LaskaKit/ESPD-35/img/004.jpg

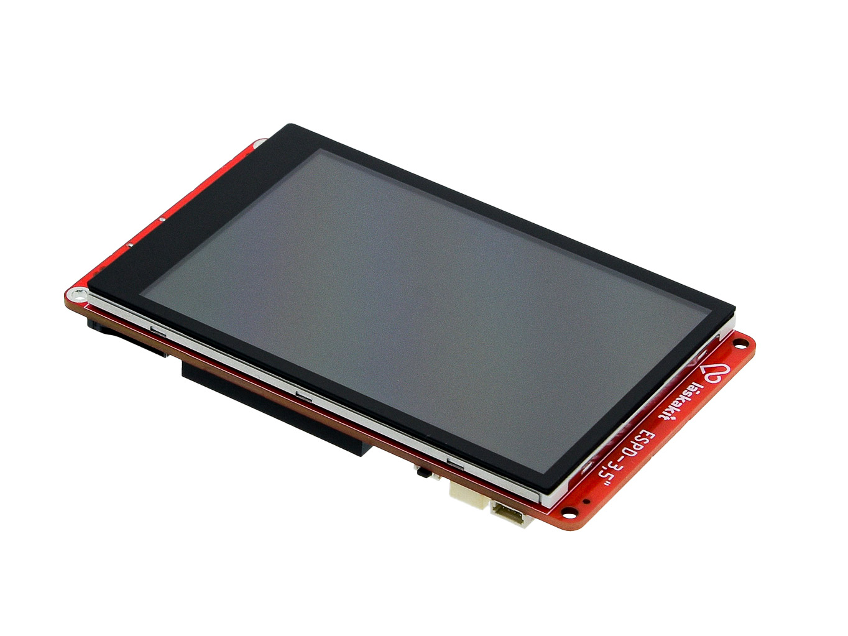
img/004.jpg
