LaskaKit/ESPD-35/img/007.JPG

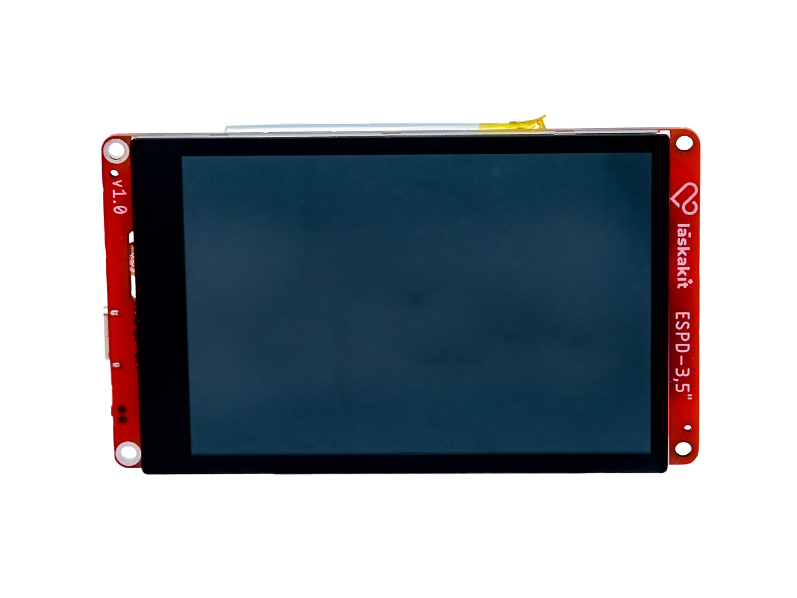
img/007.JPG
