LaskaKit/ESPD-35/SW/ESPD35_MeteoPlaneRadar/src/ADSB.cpp

// =============================================================================
//  ESPD35_MeteoPlaneRadar - ADS-B klient (stahovani dat o letadlech z adsb.fi).
//  Robustni stahovani: cele telo se nacte do PSRAM bufferu a parsuje se az
//  kompletni (kontrola utnuti proti Content-Length + jeden retry), s filtrem
//  ArduinoJson v7. Pri chybe zustava posledni dobry snimek (s_list/s_count se
//  neprepise), takze uriznuty JSON uz radar nevymaze.
//  Zdroj: adsb.fi - zdarma, bez klice, jen pro osobni nekomercni pouziti.
// =============================================================================
#include "ADSB.h"
#include <WiFi.h>
#include <WiFiClientSecure.h>
#include <HTTPClient.h>
#include <ArduinoJson.h>
#include <math.h>
#include <string.h>
#include <stdlib.h>          // strtof
#include "esp_heap_caps.h"   // PSRAM body buffer
#include "NetSink.h"         // cteni tela bezpecne vuci chunked
#include "Net.h"        // strazce interni pameti + hlavicka Date
#include "Status.h"     // jednoradkove hlaseni pro stavovou stranku
#include "Settings.h"   // vyskove pasmo, "jen s volacim znakem"
#include "Config.h"     // SQUAWK_*

static const float KM_PER_NM = 1.852f;

static Aircraft s_list[ADSB_MAX];   // posledni DOBRY snimek na obrazovce
static int s_count = 0;
// Docasny buffer, do ktereho parsujeme. Viditelny seznam (s_list/s_count) se
// prepise az po plnem a spravnem parsu - tak uriznuty JSON nikdy nevymaze radar.
static Aircraft s_tmp[ADSB_MAX];
// Ctverec vzdalenosti kazdeho letadla v s_tmp od stredu (km^2). Slouzi k tomu,
// aby se pri prekroceni ADSB_MAX drzela NEJBLIZSI letadla, ne prvnich sto
// v poradi, ve kterem je posle server (viz smycku parsovani nize).
static float s_tmpD2[ADSB_MAX];
static void (*s_poll)() = nullptr;

// Kolik letadel odfiltrovalo NASTAVENI (ne vzdalenost). Drzi se zvlast, aby
// slo na stavove strance odlisit "nad vami nic nelita" od "mate prisny filtr".
static int s_filteredOut = 0;

void ADSB_SetPollFn(void (*fn)()) { s_poll = fn; }
int  ADSB_Count() { return s_count; }
const Aircraft* ADSB_List() { return s_list; }

int ADSB_FindByHex(const char* hex) {
  if (!hex || !hex[0]) return -1;
  for (int i = 0; i < s_count; i++) {
    if (strcmp(s_list[i].hex, hex) == 0) return i;
  }
  return -1;   // uz neni v datech
}

int ADSB_FilteredOut() { return s_filteredOut; }

const char* ADSB_EmergencyCode(const Aircraft& a) {
  if (!a.squawk[0]) return nullptr;
  if (strcmp(a.squawk, SQUAWK_HIJACK) == 0) return SQUAWK_HIJACK;
  if (strcmp(a.squawk, SQUAWK_RADIO)  == 0) return SQUAWK_RADIO;
  if (strcmp(a.squawk, SQUAWK_EMERG)  == 0) return SQUAWK_EMERG;
  return nullptr;
}

// Projde letadlo uzivatelskym filtrem? Nouzovy squawk filtr PRESKAKUJE -
// letadlo hlasici 7700 je presne to, co chcete videt, i kdyz je zrovna mimo
// nastavene vyskove pasmo.
static bool passesFilter(const Aircraft& a) {
  if (Settings_SquawkAlert() && ADSB_EmergencyCode(a)) return true;
  if (Settings_OnlyWithCallsign() && !a.callsign[0]) return false;
  const uint16_t lo = Settings_AltMinFt();
  const uint16_t hi = Settings_AltMaxFt();
  // Letadlo, ktere vysku vubec nehlasi (altFt == 0), se pasmem neposuzuje -
  // jinak by ho spodni mez vyhodila, aniz by o nem cokoli bylo znamo.
  if (a.altFt > 0.0f) {
    if (a.altFt < (float)lo) return false;
    if (a.altFt > (float)hi) return false;
  }
  return true;
}

static void poll() { if (s_poll) s_poll(); }

// Cte cislo i kdyz je v JSON jako retezec.
static bool readFloat(JsonObjectConst o, const char* key, float* out) {
  JsonVariantConst v = o[key];
  if (v.is<float>() || v.is<double>() || v.is<int>()) { *out = v.as<float>(); return true; }
  if (v.is<const char*>()) {
    // ArduinoJson si ciselny retezec prevede sam, jenze atof() nerozlisi
    // chybejici hodnotu od necislne: z "ground" udelal 0.0 a ohlasil uspech.
    // Koncovy ukazatel u strtof() ten rozdil ukaze, takze necekany literal
    // propadne misto toho, aby se z nej stala nulova vyska.
    const char* str = v.as<const char*>();
    if (!str || !*str) return false;
    char* end = nullptr;
    float f = strtof(str, &end);
    if (end == str) return false;
    *out = f;
    return true;
  }
  return false;
}

// Volacka, a JEN volacka. Drive tu byl zaloznik na hex adresu, aby letadlo,
// ktere volacku nevysila (TIS-B, MLAT, soukrome a vojenske stroje), aspon neco
// ukazalo. To byla chyba: volacka jde do dotazu na trasu a hex adresa se po
// normalizaci tvari jako platne cislo letu - "a31234" se zmeni na "A31234",
// coz je Aegean Airlines 1234, takze letadlo nad Prahou hlasilo let
// Atheny - Istanbul. Bez volacky zustava pole prazdne a na trasu se nikdo
// nepta; kdo potrebuje neco vykreslit, sahne po hexu sam (viz ScreenPlanes).
static void copyCallsign(Aircraft* a, JsonObjectConst plane) {
  const char* src = plane["flight"] | "";
  while (*src == ' ' || *src == '\t') src++;   // adsb.fi doplnuje na osm znaku
  int i = 0;
  while (src[i] && i < (int)sizeof(a->callsign) - 1) { a->callsign[i] = src[i]; i++; }
  while (i > 0 && (a->callsign[i-1] == ' ' || a->callsign[i-1] == '\t')) i--;
  a->callsign[i] = '\0';
}

// -----------------------------------------------------------------------------
//  Buffer tela (PSRAM). Recykluje se mezi stazenimi, aby se interni heap
//  netristil velkym String pri kazdem pollu. Cele telo se nacte SEM pred
//  parsovanim, takze parser vzdy vidi kompletni dokument (puvodni
//  "IncompleteInput" vznikal parsovanim primo z TLS streamu, ktery skoncil
//  uprostred objektu).
// -----------------------------------------------------------------------------
static char*  s_body    = nullptr;
static size_t s_bodyCap = 0;
static const size_t ADSB_MAX_BODY = 1024 * 1024;   // 1 MB tvrdy strop
// Rezervuje se, kdyz server neposle Content-Length (chunked). Pod tvrdym
// stropem, nad vsim, co adsb.fi realne vrati: nejsirsi nabizeny dosah je
// 100 km, kde odpoved ma nizke desitky kB.
static const size_t ADSB_UNKNOWN_BODY = 384 * 1024;

static bool bodyReserve(size_t need) {
  if (need <= s_bodyCap) return true;
  size_t cap = need + 2048;
  char* nb = (char*)heap_caps_realloc(s_body, cap, MALLOC_CAP_SPIRAM);
  if (!nb) nb = (char*)heap_caps_realloc(s_body, cap, MALLOC_CAP_DEFAULT);
  if (!nb) return false;
  s_body = nb; s_bodyCap = cap;
  return true;
}

// Nacte cele telo HTTP do s_body. Vraci pocet bajtu (>= 0), nebo -1 pri tvrde
// chybe: alokace, preteceni, zaseknuti nebo prenos ukonceny driv, nez slibovala
// deklarovana delka.
static long readBody(HTTPClient& http) {
  // writeToStream() dekoduje chunked; rucni smycka nad getStreamPtr() ne, a
  // presne proto zustavaly velikosti bloku v tele.
  int declared = http.getSize();               // -1 kdyz chunked / neznamy
  if (declared > (int)ADSB_MAX_BODY) {
    Serial.printf("ADSB: hlaseno %d B, strop je %u B\n",
                  declared, (unsigned)ADSB_MAX_BODY);
    return -1;
  }
  // Sink zapisuje do pevneho bufferu a neumi ho zvetsit uprostred prenosu,
  // takze chunked odpoved musi dostat misto dopredu. Buffer lezi v PSRAM a
  // recykluje se mezi stazenimi, takze ta rezerva nic nestoji.
  size_t want = (declared > 0) ? (size_t)declared + 1 : ADSB_UNKNOWN_BODY;
  if (!bodyReserve(want)) return -1;

  return Net_ReadBody(http, (uint8_t*)s_body, s_bodyCap, "ADSB", s_poll);
}

// Filtr: parsuji se jen klice, ktere pouzivame, takze JsonDocument zustava maly
// bez ohledu na to, kolik adsb.fi posle. alt_baro MUSI zustat - nese literal
// "ground" pro detekci letadla na zemi.
static void buildFilter(JsonDocument& filter) {
  JsonObject o = filter["ac"].add<JsonObject>();   // ArduinoJson 7 idiom
  o["hex"]          = true;
  o["flight"]       = true;
  o["lat"]          = true;
  o["lon"]          = true;
  o["track"]        = true;
  o["true_heading"] = true;
  o["alt_baro"]     = true;
  o["gs"]           = true;
  o["baro_rate"]    = true;
  o["t"]            = true;
  o["r"]            = true;   // registrace - zadarmo v teze odpovedi
  o["squawk"]       = true;

  // Neni to uzitecny obsah, ale diagnostika: adsb.fi dava svuj stavovy text do
  // "msg" ("No error" pri uspechu). Filtr ho driv zahazoval, takze firmware
  // umel rict jen "chybi pole ac" a nic o tom proc. Prida se az nakonec -
  // pridani klice muze zneplatnit JsonObject vzaty vyse.
  filter["msg"] = true;
}

bool ADSB_Fetch(double lat, double lon, float radiusKm) {
  // Bez pripojeni -> nech, co je na obrazovce (radar NEVYMAZAT).
  if (WiFi.status() != WL_CONNECTED) {
    Serial.println("ADSB: no WiFi");
    Status_Set(ST_ADSB, "bez WiFi");
    return false;
  }
  // TLS handshake potrebuje ~45 kB interni RAM; bez ni selze uvnitr mbedTLS
  // a navenek to vypada jako hole "HTTP -1". Radeji poll preskocit.
  if (!Net_HeapOk("ADSB")) { Status_Set(ST_ADSB, "malo pameti"); return false; }

  float distNm = radiusKm / KM_PER_NM;
  char url[128];
  snprintf(url, sizeof(url), "%s%.5f/lon/%.5f/dist/%.1f",
           ADSB_API_BASE, lat, lon, distNm);
  Serial.printf("ADSB: %s\n", url);

  // Az dva pokusy. Jeden prechodny zadrhel (spadle TLS, uriznute telo) tak
  // nepreskoci cely cyklus; po dvou chybach se propadne a zustane posledni snimek.
  const int MAX_ATTEMPTS = 2;
  for (int attempt = 1; attempt <= MAX_ATTEMPTS; attempt++) {
    poll();
    WiFiClientSecure client;
    client.setInsecure();
    client.setHandshakeTimeout(NET_TLS_HANDSHAKE_S);

    HTTPClient http;
    http.setConnectTimeout(8000);   // ms - jen TCP connect, NE handshake
    http.setTimeout(12000);         // ms - cteni
    http.setReuse(false);
    if (!http.begin(client, url)) {
      Serial.println("ADSB: begin failed");
      if (attempt < MAX_ATTEMPTS) { delay(200); continue; }
      return false;
    }
    // Slusne se predstavit - bezplatne API adsb.fi o to zada.
    // POZOR: setUserAgent(), NE addHeader(). ESP32 HTTPClient::addHeader()
    // mlcky zahazuje Connection, Host, Accept-Encoding a prave User-Agent -
    // vidi je jako "handled by code" a nic nenahlasi. Tahle hlavicka se tedy
    // driv neposilala vubec a odchazela vychozi "ESP32HTTPClient"; adsb.lol na
    // ni odpovida 403 "User-Agent too generic". Jeden retezec pro obe API je
    // v Config.h.
    http.setUserAgent(HTTP_USER_AGENT);
    http.addHeader("Accept", "application/json");
    // Hlavicka Date je zaloha hodin, kdyz NTP neprojde (viz Clock.h).
    http.collectHeaders(NET_DATE_HEADER, 1);

    int code = http.GET();
    if (code != HTTP_CODE_OK) {
      Serial.printf("ADSB: HTTP %d (pokus %d)\n", code, attempt);
      http.end();
      if (attempt < MAX_ATTEMPTS) { delay(200); continue; }
      Status_Set(ST_ADSB, "HTTP %d", code);
      return false;   // nech posledni dobra data
    }
    Net_NoteDate(http);

    // Nacti CELE telo (do PSRAM), pak teprve parsuj - zadny parse ze streamu.
    long len = readBody(http);
    http.end();

    if (len < 0) {
      Serial.println("ADSB: cteni tela selhalo");
      if (attempt < MAX_ATTEMPTS) { delay(200); continue; }
      return false;
    }
    if (len < 8) {
      Serial.printf("ADSB: kratke telo %ld (pokus %d)\n", len, attempt);
      if (attempt < MAX_ATTEMPTS) { delay(200); continue; }
      return false;
    }

    // Levna kontrola tvaru driv, nez to uvidi parser. Chyti chybovou stranku
    // z proxy, gzip nebo zbytky bloku - tedy vsechno, co by jinak doslo az k
    // ArduinoJsonu a vratilo se jako neco nesrozumitelneho.
    const char* head = s_body;
    while (*head == ' ' || *head == '\r' || *head == '\n' || *head == '\t') head++;
    if (*head != '{') {
      Serial.printf("ADSB: odpoved nezacina JSON objektem, telo[0..120]: %.120s\n", s_body);
      Status_Set(ST_ADSB, "neocekavana odpoved");
      return false;
    }

    // Filtrovany parse kompletniho bufferu.
    JsonDocument filter;
    buildFilter(filter);
    JsonDocument doc;
    DeserializationError err =
        deserializeJson(doc, s_body, (size_t)len, DeserializationOption::Filter(filter));
    if (err) {
      Serial.printf("ADSB: JSON %s (pokus %d) - drzim poslednich %d\n",
                    err.c_str(), attempt, s_count);
      if (attempt < MAX_ATTEMPTS) { delay(200); continue; }
      return false;
    }

    if (!doc["ac"].is<JsonArray>()) {
      // Rict, CO prislo, ne jen ze to bylo spatne. "msg" je stavovy text
      // serveru, zacatek tela chyti odpovedi, ktere ocekavany tvar nemely
      // nikdy.
      Serial.printf("ADSB: chybi pole 'ac' - msg: %s\n", doc["msg"] | "(zadne msg)");
      Serial.printf("ADSB: telo[0..200]: %.200s\n", s_body);
      Status_Set(ST_ADSB, "spatny tvar odpovedi");
      return false;   // validni JSON, ale spatny tvar; retry by nepomohl
    }

    // Parsuj do DOCASNEHO seznamu; do ziveho commitni az pri uspechu.
    //
    // Pri prekroceni ADSB_MAX se NEUTINA slepe. Puvodne se pri naplneni pole
    // proste skoncilo (break), takze o tom, ktera letadla uvidite, rozhodovalo
    // poradi v odpovedi serveru - u velkeho rozsahu nad hustym provozem tak
    // mohlo vypadnout letadlo primo nad vami. Nove se drzi NEJBLIZSICH
    // ADSB_MAX letadel: po naplneni pole se nove letadlo porovna s dosud
    // nejvzdalenejsim a pripadne ho nahradi.
    const float latr0 = (float)lat * 0.0174532925f;
    const float cosLat0 = cosf(latr0);

    JsonArrayConst ac = doc["ac"].as<JsonArrayConst>();
    int   n = 0;
    int   worstIdx = -1;      // slot s nejvetsi vzdalenosti (jen kdyz je plno)
    float worstD2  = -1.0f;
    int   dropped  = 0;       // kolik letadel se nevešlo (jen pro vypis)

    s_filteredOut = 0;

    for (JsonObjectConst plane : ac) {
      float plat, plon;
      if (!readFloat(plane, "lat", &plat) || !readFloat(plane, "lon", &plon)) continue;
      // Ochrana proti nesmyslnym souradnicim (NaN projde i porovnanim, proto
      // se testuje pres !(a && b), ne pres opacnou podminku).
      if (!(plat >= -90.0f && plat <= 90.0f && plon >= -180.0f && plon <= 180.0f)) continue;
      if (plat == 0.0f && plon == 0.0f) continue;

      // Letadla NA ZEMI zahazujeme uz tady, aby nikdy nezabrala misto stroji
      // ve vzduchu. U letiste by jinak dokazala zaplnit cely ADSB_MAX.
      JsonVariantConst ab = plane["alt_baro"];
      if (ab.is<const char*>() && strcmp(ab.as<const char*>(), "ground") == 0) continue;

      // Letadlo se nejdriv poskladá CELE do docasne promenne. Az pak jde na
      // radu filtr a teprve potom se pro nej hleda misto v poli - jinak by
      // odfiltrovane letadlo stihlo zabrat slot nekomu, kdo se ma zobrazit.
      Aircraft cand;
      cand.lat = plat;
      cand.lon = plon;
      cand.onGround = false;

      // Smer letu - poznamename, jestli vubec existuje.
      float tr = 0;
      if (readFloat(plane, "track", &tr) || readFloat(plane, "true_heading", &tr)) {
        cand.track = tr;
        cand.hasTrack = true;
      } else {
        cand.track = 0;
        cand.hasTrack = false;
      }
      // Vyska (baro), rychlost, stoupani.
      float f = 0;
      cand.altFt    = readFloat(plane, "alt_baro", &f) ? f : 0;
      cand.gsKt     = readFloat(plane, "gs", &f) ? f : 0;
      cand.baroRate = readFloat(plane, "baro_rate", &f) ? f : 0;
      // Typ letadla. VYHRADNE "t" - to je kod draku ("A320"). Klic "type" je
      // ZDROJ ZPRAVY ("adsb_icao", "mlat", "tisb_icao") a jako zaloha to bylo
      // spatne: letadla, u kterych adsb.fi drak nezna, ukazovala v detailu
      // "adsb_icao" misto typu. Radsi prazdno nez nesmysl - radek se pak
      // proste nevykresli.
      const char* ty = plane["t"] | "";
      strncpy(cand.type, ty, sizeof(cand.type) - 1);
      cand.type[sizeof(cand.type) - 1] = '\0';
      // Registrace, stejna vec - "r" prijde v teze odpovedi, takze na "OK-TVU"
      // vedle typu neni potreba zadne druhe API.
      const char* rg = plane["r"] | "";
      strncpy(cand.reg, rg, sizeof(cand.reg) - 1);
      cand.reg[sizeof(cand.reg) - 1] = '\0';
      // ICAO hex - stabilni identifikator (nemeni se mezi stazenimi).
      const char* hx = plane["hex"] | "";
      strncpy(cand.hex, hx, sizeof(cand.hex) - 1);
      cand.hex[sizeof(cand.hex) - 1] = '\0';
      // Kod odpovidace. Jen ctyri osmickove cislice; cokoli jineho zahodime,
      // aby se do porovnani s 7500/7600/7700 nedostal zmetek.
      const char* sq = plane["squawk"] | "";
      if (strlen(sq) == 4 && sq[0] >= '0' && sq[0] <= '7') {
        strncpy(cand.squawk, sq, sizeof(cand.squawk) - 1);
        cand.squawk[sizeof(cand.squawk) - 1] = '\0';
      }
      copyCallsign(&cand, plane);

      // Uzivatelsky filtr (vyskove pasmo, jen s volacim znakem).
      if (!passesFilter(cand)) { s_filteredOut++; continue; }

      // Vzdalenost od stredu (km^2, plocha azimutalni aproximace - staci nam
      // na porovnavani, nemusi byt presna).
      float dx = (plon - (float)lon) * 111.0f * cosLat0;
      float dy = (plat - (float)lat) * 111.0f;
      float d2 = dx * dx + dy * dy;

      int slot;
      if (n < ADSB_MAX) {
        slot = n++;
      } else {
        if (worstIdx < 0) {   // dopocitat nejvzdalenejsi az kdyz je poprve plno
          worstD2 = -1.0f;
          for (int i = 0; i < ADSB_MAX; i++)
            if (s_tmpD2[i] > worstD2) { worstD2 = s_tmpD2[i]; worstIdx = i; }
        }
        dropped++;
        if (d2 >= worstD2) continue;   // dal nez nejvzdalenejsi -> nezajima nas
        slot = worstIdx;
        worstIdx = -1;                 // po nahrazeni se musi najit znovu
      }

      s_tmpD2[slot] = d2;
      s_tmp[slot] = cand;
    }

    // Commitni docasny snimek do ziveho seznamu naraz.
    for (int i = 0; i < n; i++) s_list[i] = s_tmp[i];
    s_count = n;
    if (dropped) Serial.printf("Letadla: %d (%ld bajtu, %d vzdalenych vynechano)\n",
                               n, len, dropped);
    else         Serial.printf("Letadla: %d (%ld bajtu)\n", n, len);
    if (s_filteredOut) Serial.printf("Letadla: %d odfiltrovano nastavenim\n", s_filteredOut);

    if (s_filteredOut) Status_Set(ST_ADSB, "OK, %d letadel (%d filtrem)", n, s_filteredOut);
    else               Status_Set(ST_ADSB, "OK, %d letadel", n);
    return true;
  }
  Status_Set(ST_ADSB, "stahovani selhalo");
  return false;
}
