LaskaKit/ESPD-35/SW/ESPD35_sensor_matrix_MF/DSEG14Classic_100px_bold.h

// Created by http://oleddisplay.squix.ch/ Consider a donation
// In case of problems make sure that you are using the font file with the correct version!
const uint8_t DSEG14_Classic_Bold_100Bitmaps[] PROGMEM = {

	// Bitmap Data:
	0x00, // ' '
	0x00, // '!'
	0x00,0x00,0x00,0x00,0x01,0x80,0x00,0x00,0x00,0x1E,0x00,0x00,0x00,0x01,0xF8,0x00,0x00,0x00,0x0F,0xE0,0x00,0x00,0x00,0x7F,0x80,0x00,0x00,0x03,0xFE,0x00,0x00,0x00,0x1F,0xF8,0x00,0x00,0x00,0xFF,0xE0,0x00,0x00,0x07,0xFF,0x80,0x00,0x00,0x3F,0xFC,0x00,0x1F,0xFF,0xFF,0xE0,0x00,0xFF,0xFF,0xFF,0x00,0x07,0xFF,0xFF,0xF8,0x00,0x3F,0xFF,0xFF,0xC0,0x01,0xFF,0xFF,0xFE,0x00,0x0F,0xFF,0xFF,0xF0,0x00,0x7F,0xFF,0xFF,0x80,0x03,0xFF,0xFF,0xFC,0x00,0x1F,0xFF,0xFF,0xE0,0x00,0xFF,0xFF,0xFF,0x00,0x07,0xFF,0xFF,0xF8,0x00,0x3F,0xFF,0xFF,0xC0,0x01,0xFF,0xFF,0xFE,0x00,0x0F,0xFF,0xFF,0xF0,0x00,0x7F,0xFF,0xFF,0x80,0x03,0xFF,0xFF,0xFC,0x00,0x1F,0xFF,0xFF,0xE0,0x00,0xFF,0xFF,0xFF,0x00,0x07,0xFF,0xFF,0xF8,0x00,0x3F,0xFF,0xFF,0xC0,0x01,0xFF,0xFF,0xFE,0x00,0x0F,0xFF,0xFF,0xF0,0x00,0x7F,0xFF,0xFF,0x80,0x03,0xFF,0xFF,0xFC,0x00,0x1F,0xFD,0xFF,0xE0,0x00,0x7F,0xEF,0xFF,0x00,0x01,0xFE,0x7F,0xF8,0x00,0x0F,0xF3,0xFF,0xC0,0x00,0x3F,0x1F,0xFC,0x00,0x01,0xF0,0xFF,0xC0,0x00,0x07,0x87,0xFC,0x00,0x00,0x38,0x3F,0xC0,0x00,0x00,0xC1,0xFC,0x00,0x00,0x00,0x0F,0xC0,0x00,0x00,0x00,0x00, // '"'
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
,0xFF,0xE0,0x01,0xFF,0xF0,0x00,0x00,0x07,0xFF,0x80,0x07,0xFF,0xC0,0x00,0x00,0x1F,0xFE,0x00,0x1F,0xFF,0x00,0x00,0x00,0x7F,0xF8,0x00,0x7F,0xFC,0x00,0x00,0x01,0xFF,0xE0,0x01,0xFF,0xF0,0x00,0x00,0x07,0xFF,0x80,0x07,0xFF,0xC0,0x00,0x00,0x1F,0xFE,0x00,0x1F,0xFF,0x00,0x00,0x00,0x7F,0xF8,0x00,0x7F,0xFC,0x00,0x00,0x01,0xFF,0xE0,0x01,0xFF,0xF0,0x00,0x00,0x00,0x00,0x00,0x03,0xFF,0xC0,0x00,0x00,0x00,0x00,0x00,0x07,0xFF,0x00,0x07,0xFF,0xFF,0xFF,0xFF,0x8F,0xFC,0x00,0x3F,0xFF,0xFF,0xFF,0xFF,0x1F,0xF0,0x01,0xFF,0xFF,0xFF,0xFF,0xFE,0x3F,0xC0,0x0F,0xFF,0xFF,0xFF,0xFF,0xFC,0x7F,0x00,0x7F,0xFF,0xFF,0xFF,0xFF,0xF8,0xFC,0x03,0xFF,0xFF,0xFF,0xFF,0xFF,0xF1,0xE0,0x1F,0xFF,0xFF,0xFF,0xFF,0xFF,0xE3,0x00,0xFF,0xFF,0xFF,0xFF,0xFF,0xFF,0xC0,0x07,0xFF,0xFF,0xFF,0xFF,0xFF,0xFF,0x80,0x1F,0xFF,0xFF,0xFF,0xFF,0xFF,0xFE,0x00,0x3F,0xFF,0xFF,0xFF,0xFF,0xFF,0xF0,0x00,0x7F,0xFF,0xFF,0xFF,0xFF,0xFF,0x80, // '$'
	0x00,0x00,0x00,0x00,0x00,0x00,0x00,0x00,0xC0,0x00,0x00,0x00,0x00,0x00,0x00,0x07,0x80,0x00,0x00,0x00,0x00,0x00,0x00,0x3F,0x00,0x00,0x00,0x00,0x00,0x00,0x00,0xFE,0x00,0x00,0x00,0x00,0x00,0x00,0x03,0xFC,0x00,0x00,0x00,0x00,0x00,0x00,0x0F,0xF8,0x00,0x00,0x00,0x00,0x00,0x00,0x3F,0xF0,0x00,0x00,0x00,0x00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
	0x1F,0xFF,0xFF,0xFF,0xFF,0xFF,0xE0,0x0F,0xFF,0xFF,0xFF,0xFF,0xFF,0xFC,0x07,0xFF,0xFF,0xFF,0xFF,0xFF,0xFF,0x81,0xFF,0xFF,0xFF,0xFF,0xFF,0xFF,0xE0,0x3F,0xFF,0xFF,0xFF,0xFF,0xFF,0xF0,0x07,0xFF,0xFF,0xFF,0xFF,0xFF,0xF8,0x00,0xFF,0xFF,0xFF,0xFF,0xFF,0xFC,0x00,0x1F,0xFF,0xFF,0xFF,0xFF,0xFE,0x00,0x03,0xFF,0xFF,0xFF,0xFF,0xFF,0x00,0x00,0x7F,0xFF,0xFF,0xFF,0xFF,0x80,0x00,0x0F,0xFF,0xFF,0xFF,0xFF,0xC0,0x00,0x01,0xFF,0xFF,0xFF,0xFF,0xE0,0x00,0x00,0x00,0x00,0x00,0x00,0x00,0x00,0x00,0x00,0x00,0x00,0x00,0x00,0x00,0x00,0x03,0x80,0x00,0x00,0x0E,0x00,0x00,0x00,0xF0,0x00,0x00,0x03,0x80,0x00,0x00,0x3E,0x00,0x00,0x01,0xE0,0x00,0x00,0x0F,0x80,0x00,0x00,0xF8,0x00,0x00,0x03,0xF0,0x00,0x00,0x3E,0x00,0x00,0x00,0xFC,0x00,0x00,0x1F,0x80,0x00,0x00,0x3F,0x80,0x00,0x07,0xE0,0x00,0x00,0x0F,0xE0,0x00,0x03,0xF8,0x00,0x00,0x03,0xFC,0x00,0x00,0xFE,0x00,0x00,0x00,0xFF,0x80,0x00,0x7F,0x80,0x00,0x00,0x3F,0xE0,0x00,0x1F,0xE0,0x00,0x00,0x0F,0xF8,0x00,0x07,0xF8,0x00,0x00,0x03,0xFE,0x00,0x01,0xFE,0x00,0x00,0x00,0xFF,0x80,0x00,0x7F,0x80,0x00,0x00,0x3F,0xE0,0x00,0x1F,0xE0,0x00,0x00,0x0F,0xF8,0x00,0x07,0xF8,0x00,0x00,0x03,0xFE,0x00,0x01,0xFE,0x00,0x00,0x00,0xFF,0x80,0x00,0x7F,0x80,0x00,0x00,0x3F,0xE0,0x00,0x1F,0xE0,0x00,0x00,0x0F,0xF8,0x00,0x07,0xF8,0x00,0x00,0x01,0xFE,0x00,0x01,0xFE,0x00,0x00,0x00,0x7F,0x80,0x00,0x7F,0x00,0x00,0x00,0x0F,0xE0,0x00,0x1F,0xC0,0x00,0x00,0x03,0xF8,0x00,0x07,0xE0,0x00,0x00,0x00,0x7E,0x00,0x01,0xF8,0x00,0x00,0x00,0x0F,0x80,0x00,0x7C,0x00,0x00,0x00,0x03,0xE0,0x00,0x1E,0x00,0x00,0x00,0x00,0x78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
,0x00,0x00,0x00,0x00,0x0F,0xFF,0x00,0x00,0x00,0x00,0x00,0x00,0x3F,0xFC,0x00,0x00,0x00,0x00,0x00,0x00,0xFF,0xF0,0x00,0x00,0x00,0x00,0x00,0x03,0xFF,0xC0,0x00,0x00,0x00,0x00,0x00,0x0F,0xFF,0x00,0x00,0x00,0x00,0x00,0x00,0x3F,0xFC,0x00,0x00,0x00,0x00,0x00,0x00,0xFF,0xF0,0x00,0x00,0x00,0x00,0x00,0x03,0xFF,0xC0,0x00,0x00,0x00,0x00,0x00,0x0F,0xFF,0x00,0x00,0x00,0x00,0x00,0x00,0x3F,0xF8,0x00,0x00,0x00,0x00,0x00,0x00,0xFF,0xC7,0xFF,0xFF,0xFF,0xFF,0x80,0x03,0xFE,0x3F,0xFF,0xFF,0xFF,0xFF,0x00,0x0F,0xF1,0xFF,0xFF,0xFF,0xFF,0xFE,0x00,0x3F,0x8F,0xFF,0xFF,0xFF,0xFF,0xFC,0x00,0xFC,0x7F,0xFF,0xFF,0xFF,0xFF,0xF8,0x01,0xE3,0xFF,0xFF,0xFF,0xFF,0xFF,0xF0,0x03,0x1F,0xFF,0xFF,0xFF,0xFF,0xFF,0xE0,0x00,0xFF,0xFF,0xFF,0xFF,0xFF,0xFF,0xC0,0x07,0xFF,0xFF,0xFF,0xFF,0xFF,0xFF,0x80,0x1F,0xFF,0xFF,0xFF,0xFF,0xFF,0xFE,0x00,0x3F,0xFF,0xFF,0xFF,0xFF,0xFF,0xF0,0x00,0x7F,0xFF,0xFF,0xFF,0xFF,0xFF,0x80, // '2'
	0x1F,0xFF,0xFF,0xFF,0xFF,0xFF,0xE0,0x0F,0xFF,0xFF,0xFF,0xFF,0xFF,0xFC,0x07,0xFF,0xFF,0xFF,0xFF,0xFF,0xFF,0x81,0xFF,0xFF,0xFF,0xFF,0xFF,0xFF,0xE0,0x3F,0xFF,0xFF,0xFF,0xFF,0xFF,0xF0,0x07,0xFF,0xFF,0xFF,0xFF,0xFF,0xF8,0xC0,0xFF,0xFF,0xFF,0xFF,0xFF,0xFC,0x78,0x1F,0xFF,0xFF,0xFF,0xFF,0xFE,0x3F,0x03,0xFF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
	0x00,0x00,0x00,0x00,0x00,0x00,0x00,0x00,0xC0,0x00,0x00,0x00,0x00,0x00,0x00,0xC7,0x80,0x00,0x00,0x00,0x00,0x00,0x07,0xBF,0x00,0x00,0x00,0x00,0x00,0x00,0x3F,0xFE,0x00,0x00,0x00,0x00,0x00,0x01,0xFF,0xFC,0x00,0x00,0x00,0x00,0x00,0x0F,0xFF,0xF8,0x00,0x00,0x00,0x00,0x00,0x7F,0xFF,0xF0,0x00,0x00,0x00,0x00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
	0x01,0xFF,0xFF,0xFF,0xFF,0xFF,0xFE,0x00,0x0F,0xFF,0xFF,0xFF,0xFF,0xFF,0xFC,0x00,0x7F,0xFF,0xFF,0xFF,0xFF,0xFF,0xF8,0x01,0xFF,0xFF,0xFF,0xFF,0xFF,0xFF,0xE0,0x03,0xFF,0xFF,0xFF,0xFF,0xFF,0xFF,0x00,0xC7,0xFF,0xFF,0xFF,0xFF,0xFF,0xF8,0x07,0x8F,0xFF,0xFF,0xFF,0xFF,0xFF,0xC0,0x3F,0x1F,0xFF,0xFF,0xFF,0xFF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
	0x01,0xFF,0xFF,0xFF,0xFF,0xFF,0xFE,0x00,0x0F,0xFF,0xFF,0xFF,0xFF,0xFF,0xFC,0x00,0x7F,0xFF,0xFF,0xFF,0xFF,0xFF,0xF8,0x01,0xFF,0xFF,0xFF,0xFF,0xFF,0xFF,0xE0,0x03,0xFF,0xFF,0xFF,0xFF,0xFF,0xFF,0x00,0xC7,0xFF,0xFF,0xFF,0xFF,0xFF,0xF8,0x07,0x8F,0xFF,0xFF,0xFF,0xFF,0xFF,0xC0,0x3F,0x1F,0xFF,0xFF,0xFF,0xFF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
	0x01,0xFF,0xFF,0xFF,0xFF,0xFF,0xFE,0x00,0x0F,0xFF,0xFF,0xFF,0xFF,0xFF,0xFC,0x00,0x7F,0xFF,0xFF,0xFF,0xFF,0xFF,0xF8,0x01,0xFF,0xFF,0xFF,0xFF,0xFF,0xFF,0xE0,0x03,0xFF,0xFF,0xFF,0xFF,0xFF,0xFF,0x00,0xC7,0xFF,0xFF,0xFF,0xFF,0xFF,0xF8,0xC7,0x8F,0xFF,0xFF,0xFF,0xFF,0xFF,0xC7,0xBF,0x1F,0xFF,0xFF,0xFF,0xFF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
	0x01,0xFF,0xFF,0xFF,0xFF,0xFF,0xFE,0x00,0x0F,0xFF,0xFF,0xFF,0xFF,0xFF,0xFC,0x00,0x7F,0xFF,0xFF,0xFF,0xFF,0xFF,0xF8,0x01,0xFF,0xFF,0xFF,0xFF,0xFF,0xFF,0xE0,0x03,0xFF,0xFF,0xFF,0xFF,0xFF,0xFF,0x00,0xC7,0xFF,0xFF,0xFF,0xFF,0xFF,0xF8,0xC7,0x8F,0xFF,0xFF,0xFF,0xFF,0xFF,0xC7,0xBF,0x1F,0xFF,0xFF,0xFF,0xFF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
	0x01,0xFF,0xFF,0xFF,0xFF,0xFF,0xFE,0x00,0x0F,0xFF,0xFF,0xFF,0xFF,0xFF,0xFC,0x00,0x7F,0xFF,0xFF,0xFF,0xFF,0xFF,0xF8,0x01,0xFF,0xFF,0xFF,0xFF,0xFF,0xFF,0xE0,0x03,0xFF,0xFF,0xFF,0xFF,0xFF,0xFF,0x00,0xC7,0xFF,0xFF,0xFF,0xFF,0xFF,0xF8,0xC7,0x8F,0xFF,0xFF,0xFF,0xFF,0xFF,0xC7,0xBF,0x1F,0xFF,0xFF,0xFF,0xFF,0xFE,0x3F,0xFE,0x3F,0xFF,0xFF,0xFF,0xFF,0xF1,0xFF,0xFC,0x7F,0xFF,0xFF,0xFF,0xFF,0x8F,0xFF,0xF8,0xFF,0xFF,0xFF,0xFF,0xFC,0x7F,0xFF,0xF1,0xFF,0xFF,0xFF,0xFF,0xE3,0xFF,0xFF,0xE0,0x00,0x00,0x00,0x00,0x1F,0xFF,0xFF,0xC0,0x00,0x00,0x00,0x00,0xFF,0xFF,0xFF,0x00,0x00,0x00,0x00,0x07,0xFF,0xFF,0xFC,0x00,0x00,0x00,0x00,0x1F,0xFF,0xFF,0xF0,0x00,0x00,0x00,0x00,0x7F,0xFF,0xFF,0xC0,0x00,0x00,0x00,0x01,0xFF,0xFF,0xFF,0x00,0x00,0x00,0x00,0x07,0xFF,0xFF,0xFC,0x00,0x00,0x00,0x00,0x1F,0xFF,0xFF,0xF0,0x00,0x00,0x00,0x00,0x7F,0xFF,0xFF,0xC0,0x00,0x00,0x00,0x01,0xFF,0xFF,0xFF,0x00,0x00,0x00,0x00,0x07,0xFF,0xFF,0xFC,0x00,0x00,0x00,0x00,0x1F,0xFF,0xFF,0xF0,0x00,0x00,0x00,0x00,0x7F,0xFF,0xFF,0xC0,0x00,0x00,0x00,0x01,0xFF,0xFF,0xFF,0x00,0x00,0x00,0x00,0x07,0xFF,0xFF,0xFC,0x00,0x00,0x00,0x00,0x1F,0xFF,0xFF,0xF0,0x00,0x00,0x00,0x00,0x7F,0xFF,0xFF,0xC0,0x00,0x00,0x00,0x01,0xFF,0xFF,0xFF,0x00,0x00,0x00,0x00,0x07,0xFF,0xFF,0xFC,0x00,0x00,0x00,0x00,0x1F,0xFF,0xFF,0xF0,0x00,0x00,0x00,0x00,0x7F,0xFF,0xFF,0xC0,0x00,0x00,0x00,0x01,0xFF,0xFF,0xFF,0x00,0x00,0x00,0x00,0x07,0xFF,0xFF,0xFC,0x00,0x00,0x00,0x00,0x1F,0xFF,0xFF,0xF0,0x00,0x00,0x00,0x00,0x7F,0xFF,0xFF,0xC0,0x00,0x00,0x00,0x01,0xFF,0xFF,0xFF,0x00,0x00,0x00,0x00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
,0xFF,0xE0,0x00,0x00,0x00,0x00,0x00,0x07,0xFF,0x80,0x00,0x00,0x00,0x00,0x00,0x1F,0xFE,0x00,0x00,0x00,0x00,0x00,0x00,0x7F,0xF8,0x00,0x00,0x00,0x00,0x00,0x01,0xFF,0xE0,0x00,0x00,0x00,0x00,0x00,0x07,0xFF,0x80,0x00,0x00,0x00,0x00,0x00,0x1F,0xFE,0x00,0x00,0x00,0x00,0x00,0x00,0x7F,0xF8,0x00,0x00,0x00,0x00,0x00,0x01,0xFF,0xE0,0x00,0x00,0x00, // '?'
	0x01,0xFF,0xFF,0xFF,0xFF,0xFF,0xFE,0x00,0x0F,0xFF,0xFF,0xFF,0xFF,0xFF,0xFC,0x00,0x7F,0xFF,0xFF,0xFF,0xFF,0xFF,0xF8,0x01,0xFF,0xFF,0xFF,0xFF,0xFF,0xFF,0xE0,0x03,0xFF,0xFF,0xFF,0xFF,0xFF,0xFF,0x00,0xC7,0xFF,0xFF,0xFF,0xFF,0xFF,0xF8,0xC7,0x8F,0xFF,0xFF,0xFF,0xFF,0xFF,0xC7,0xBF,0x1F,0xFF,0xFF,0xFF,0xFF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
	0x01,0xFF,0xFF,0xFF,0xFF,0xFF,0xFE,0x00,0x0F,0xFF,0xFF,0xFF,0xFF,0xFF,0xFC,0x00,0x7F,0xFF,0xFF,0xFF,0xFF,0xFF,0xF8,0x01,0xFF,0xFF,0xFF,0xFF,0xFF,0xFF,0xE0,0x03,0xFF,0xFF,0xFF,0xFF,0xFF,0xFF,0x00,0xC7,0xFF,0xFF,0xFF,0xFF,0xFF,0xF8,0xC7,0x8F,0xFF,0xFF,0xFF,0xFF,0xFF,0xC7,0xBF,0x1F,0xFF,0xFF,0xFF,0xFF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
	0x1F,0xFF,0xFF,0xFF,0xFF,0xFF,0xE0,0x0F,0xFF,0xFF,0xFF,0xFF,0xFF,0xFC,0x07,0xFF,0xFF,0xFF,0xFF,0xFF,0xFF,0x81,0xFF,0xFF,0xFF,0xFF,0xFF,0xFF,0xE0,0x3F,0xFF,0xFF,0xFF,0xFF,0xFF,0xF0,0x07,0xFF,0xFF,0xFF,0xFF,0xFF,0xF8,0xC0,0xFF,0xFF,0xFF,0xFF,0xFF,0xFC,0x78,0x1F,0xFF,0xFF,0xFF,0xFF,0xFE,0x3F,0x03,0xFF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
	0x01,0xFF,0xFF,0xFF,0xFF,0xFF,0xFE,0x01,0xFF,0xFF,0xFF,0xFF,0xFF,0xFF,0x81,0xFF,0xFF,0xFF,0xFF,0xFF,0xFF,0xE0,0xFF,0xFF,0xFF,0xFF,0xFF,0xFF,0xF0,0x3F,0xFF,0xFF,0xFF,0xFF,0xFF,0xF1,0x8F,0xFF,0xFF,0xFF,0xFF,0xFF,0xF1,0xE3,0xFF,0xFF,0xFF,0xFF,0xFF,0xF1,0xF8,0xFF,0xFF,0xFF,0xFF,0xFF,0xF0,0xFE,0x3F,0xFF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
	0x1F,0xFF,0xFF,0xFF,0xFF,0xFF,0xE0,0x0F,0xFF,0xFF,0xFF,0xFF,0xFF,0xFC,0x07,0xFF,0xFF,0xFF,0xFF,0xFF,0xFF,0x81,0xFF,0xFF,0xFF,0xFF,0xFF,0xFF,0xE0,0x3F,0xFF,0xFF,0xFF,0xFF,0xFF,0xF0,0x07,0xFF,0xFF,0xFF,0xFF,0xFF,0xF8,0xC0,0xFF,0xFF,0xFF,0xFF,0xFF,0xFC,0x78,0x1F,0xFF,0xFF,0xFF,0xFF,0xFE,0x3F,0x03,0xFF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
	0x01,0xFF,0xFF,0xFF,0xFF,0xFF,0xFE,0x01,0xFF,0xFF,0xFF,0xFF,0xFF,0xFF,0x81,0xFF,0xFF,0xFF,0xFF,0xFF,0xFF,0xE0,0xFF,0xFF,0xFF,0xFF,0xFF,0xFF,0xF0,0x3F,0xFF,0xFF,0xFF,0xFF,0xFF,0xF1,0x8F,0xFF,0xFF,0xFF,0xFF,0xFF,0xF1,0xE3,0xFF,0xFF,0xFF,0xFF,0xFF,0xF1,0xF8,0xFF,0xFF,0xFF,0xFF,0xFF,0xF0,0xFE,0x3F,0xFF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
	0x01,0xFF,0xFF,0xFF,0xFF,0xFF,0xFE,0x01,0xFF,0xFF,0xFF,0xFF,0xFF,0xFF,0x81,0xFF,0xFF,0xFF,0xFF,0xFF,0xFF,0xE0,0xFF,0xFF,0xFF,0xFF,0xFF,0xFF,0xF0,0x3F,0xFF,0xFF,0xFF,0xFF,0xFF,0xF1,0x8F,0xFF,0xFF,0xFF,0xFF,0xFF,0xF1,0xE3,0xFF,0xFF,0xFF,0xFF,0xFF,0xF1,0xF8,0xFF,0xFF,0xFF,0xFF,0xFF,0xF0,0xFE,0x3F,0xFF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
	0x01,0xFF,0xFF,0xFF,0xFF,0xFF,0xFE,0x00,0x0F,0xFF,0xFF,0xFF,0xFF,0xFF,0xFC,0x00,0x7F,0xFF,0xFF,0xFF,0xFF,0xFF,0xF8,0x01,0xFF,0xFF,0xFF,0xFF,0xFF,0xFF,0xE0,0x03,0xFF,0xFF,0xFF,0xFF,0xFF,0xFF,0x00,0xC7,0xFF,0xFF,0xFF,0xFF,0xFF,0xF8,0x07,0x8F,0xFF,0xFF,0xFF,0xFF,0xFF,0xC0,0x3F,0x1F,0xFF,0xFF,0xFF,0xFF,0xFE,0x00,0xFE,0x3F,0xFF,0xFF,0xFF,0xFF,0xF0,0x03,0xFC,0x7F,0xFF,0xFF,0xFF,0xFF,0x80,0x0F,0xF8,0xFF,0xFF,0xFF,0xFF,0xFC,0x00,0x3F,0xF1,0xFF,0xFF,0xFF,0xFF,0xE0,0x00,0xFF,0xE0,0x00,0x00,0x00,0x00,0x00,0x03,0xFF,0xC0,0x00,0x00,0x00,0x00,0x00,0x0F,0xFF,0x00,0x00,0x00,0x00,0x00,0x00,0x3F,0xFC,0x00,0x00,0x00,0x00,0x00,0x00,0xFF,0xF0,0x00,0x00,0x00,0x00,0x00,0x03,0xFF,0xC0,0x00,0x00,0x00,0x00,0x00,0x0F,0xFF,0x00,0x00,0x00,0x00,0x00,0x00,0x3F,0xFC,0x00,0x00,0x00,0x00,0x00,0x00,0xFF,0xF0,0x00,0x00,0x00,0x00,0x00,0x03,0xFF,0xC0,0x00,0x00,0x00,0x00,0x00,0x0F,0xFF,0x00,0x00,0x00,0x00,0x00,0x00,0x3F,0xFC,0x00,0x00,0x00,0x00,0x00,0x00,0xFF,0xF0,0x00,0x00,0x00,0x00,0x00,0x03,0xFF,0xC0,0x00,0x00,0x00,0x00,0x00,0x0F,0xFF,0x00,0x00,0x00,0x00,0x00,0x00,0x3F,0xFC,0x00,0x00,0x00,0x00,0x00,0x00,0xFF,0xF0,0x00,0x00,0x00,0x00,0x00,0x03,0xFF,0xC0,0x00,0x00,0x00,0x00,0x00,0x0F,0xFF,0x00,0x00,0x00,0x00,0x00,0x00,0x3F,0xFC,0x00,0x00,0x00,0x00,0x00,0x00,0xFF,0xF0,0x00,0x00,0x00,0x00,0x00,0x03,0xFF,0xC0,0x00,0x00,0x00,0x00,0x00,0x0F,0xFF,0x00,0x00,0x00,0x00,0x00,0x00,0x3F,0xFC,0x00,0x00,0x00,0x00,0x00,0x00,0xFF,0xF0,0x00,0x00,0x00,0x00,0x00,0x03,0xFF,0xC0,0x00,0x00,0x00,0x00,0x00,0x0F,0xFF,0x00,0x00,0x00,0x00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
	  { 15806,  57, 100,  83,   10, -100 }, // 'C'
	  { 16519,  58, 100,  83,   14, -100 }, // 'D'
	  { 17244,  57, 100,  83,   10, -100 }, // 'E'
	  { 17957,  57,  96,  83,   10, -100 }, // 'F'
	  { 18641,  62, 100,  83,   10, -100 }, // 'G'
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
};
const GFXfont DSEG14_Classic_Bold_100 PROGMEM = {
(uint8_t  *)DSEG14_Classic_Bold_100Bitmaps,(GFXglyph *)DSEG14_Classic_Bold_100Glyphs,0x20, 0x7E, 109};
