LaskaKit/ESPD-35/SW/ESPD35_sensor_matrix_MF/DSEG14Classic_60px_bold.h

// Created by http://oleddisplay.squix.ch/ Consider a donation
// In case of problems make sure that you are using the font file with the correct version!
const uint8_t DSEG14_Classic_Bold_60Bitmaps[] PROGMEM = {

	// Bitmap Data:
	0x00, // ' '
	0x00, // '!'
	0x60,0x00,0x03,0xC0,0x00,0x0F,0x80,0x00,0x3F,0x00,0x00,0xFE,0x00,0x03,0xF8,0x00,0x0F,0xE0,0x1F,0xFF,0x80,0x7F,0xFE,0x01,0xFF,0xF8,0x07,0xFF,0xE0,0x1F,0xFF,0x80,0x7F,0xFE,0x01,0xFF,0xF8,0x07,0xFF,0xE0,0x1F,0xFF,0x80,0x7F,0xFE,0x01,0xFF,0xF8,0x07,0xFF,0xE0,0x1F,0xFF,0x80,0x7F,0xFE,0x01,0xFF,0xF8,0x03,0xEF,0xE0,0x07,0x3F,0x00,0x1C,0xF8,0x00,0x23,0xC0,0x00,0x80, // '"'
	0xFF,0xFF,0xFF,0xFF,0xC0,0x03,0xC0,0x03,0xC0,0x03,0xC0,0x03,0xC0,0x03,0xC0,0x03,0xC0,0x03,0xC0,0x03,0xC0,0x03,0xC0,0x03,0xC0,0x03,0xC0,0x03,0xC0,0x03,0xC0,0x03,0xC0,0x03,0xC0,0x03,0xC0,0x03,0xC0,0x03,0xC0,0x03,0xC0,0x03,0xC0,0x03,0xC0,0x03,0xC0,0x03,0xC0,0x03,0xC0,0x03,0xC0,0x03,0xC0,0x03,0xC0,0x03,0xC0,0x03,0xC0,0x03,0xC0,0x03,0xC0,0x03,0xC0,0x03,0xC0,0x03,0xC0,0x03,0xC0,0x03,0xFF,0xFF,0xFF,0xFF, // '#'
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
	  {  6116,  34,  60,  50,    6,  -60 }, // 'E'
	  {  6371,  34,  57,  50,    6,  -60 }, // 'F'
	  {  6614,  37,  60,  50,    6,  -60 }, // 'G'
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
};
const GFXfont DSEG14_Classic_Bold_60 PROGMEM = {
(uint8_t  *)DSEG14_Classic_Bold_60Bitmaps,(GFXglyph *)DSEG14_Classic_Bold_60Glyphs,0x20, 0x7E, 66};
