LaskaKit/ESPD-35/SW/ESPD35_sensor_matrix_MF/DSEG14Classic_80px_bold.h

// Created by http://oleddisplay.squix.ch/ Consider a donation
// In case of problems make sure that you are using the font file with the correct version!
const uint8_t DSEG14_Classic_Bold_80Bitmaps[] PROGMEM = {

	// Bitmap Data:
	0x00, // ' '
	0x00, // '!'
	0x60,0x00,0x00,0x03,0xC0,0x00,0x00,0x0F,0x80,0x00,0x00,0x3F,0x00,0x00,0x00,0xFE,0x00,0x00,0x03,0xFC,0x00,0x00,0x0F,0xF8,0x00,0x00,0x3F,0xF0,0x00,0x00,0xFF,0xC0,0x0F,0xFF,0xFF,0x00,0x3F,0xFF,0xFC,0x00,0xFF,0xFF,0xF0,0x03,0xFF,0xFF,0xC0,0x0F,0xFF,0xFF,0x00,0x3F,0xFF,0xFC,0x00,0xFF,0xFF,0xF0,0x03,0xFF,0xFF,0xC0,0x0F,0xFF,0xFF,0x00,0x3F,0xFF,0xFC,0x00,0xFF,0xFF,0xF0,0x03,0xFF,0xFF,0xC0,0x0F,0xFF,0xFF,0x00,0x3F,0xFF,0xFC,0x00,0xFF,0xFF,0xF0,0x03,0xFF,0xFF,0xC0,0x0F,0xFF,0xFF,0x00,0x3F,0xFF,0xFC,0x00,0xFF,0xBF,0xF0,0x01,0xFE,0xFF,0xC0,0x07,0xF3,0xFF,0x00,0x0F,0x8F,0xF8,0x00,0x3E,0x3F,0xC0,0x00,0x70,0xFE,0x00,0x00,0xC3,0xF0,0x00,0x02,0x0F,0x80,0x00,0x00,0x00, // '"'
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
